DgFutureLab/satoyama-node/data/first_deployment/Battery Discharge.png

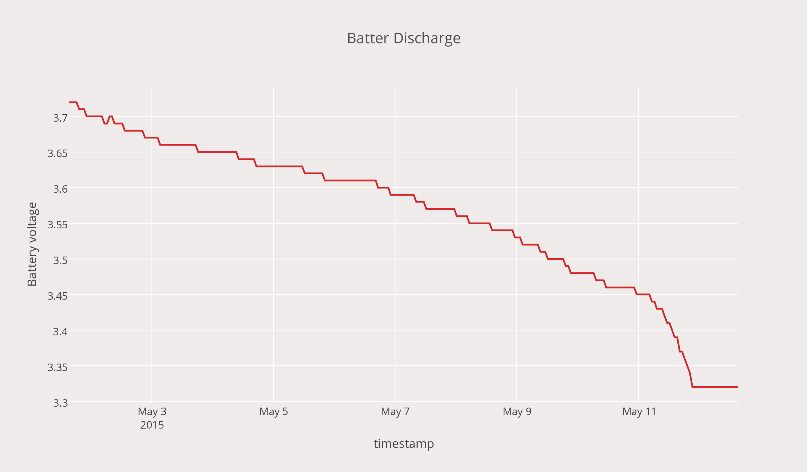
data/first_deployment/Battery Discharge.png
