DgFutureLab/satoyama-node/data/first_deployment/TechRice Alpha Field Water Level.png

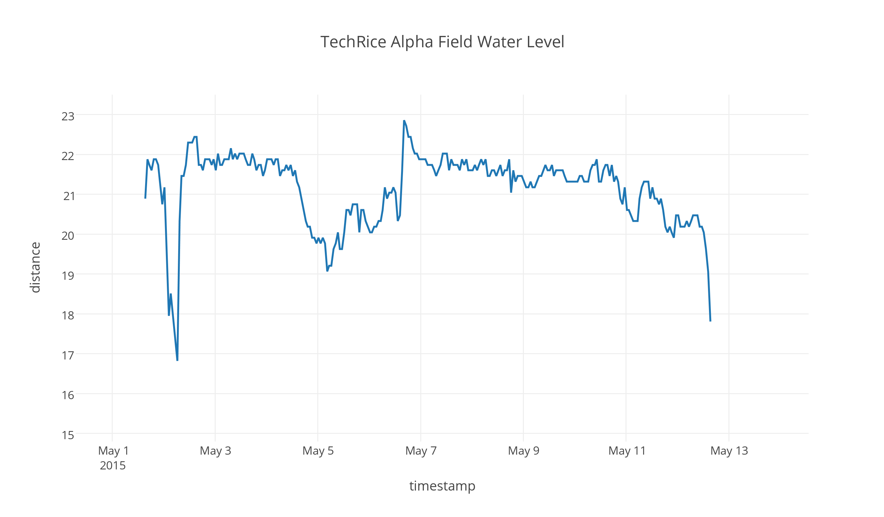
data/first_deployment/TechRice Alpha Field Water Level.png
