DgFutureLab/satoyama-node/hardware/range_finder/design1/simulation/TX/TX.asc

C1: cap; 0.01µF
Q1: npn; 2N2222
R1: res; 1.8k
R2: res; 1.8k
R3: res; 5.6k
R4: res; 470
R5: res; 220
R6: res; 400
U1: NE555
V5: voltage; 5
Named nets: 0, Vout, V5, Vpulse, e, b, c
.tran 0 200us 0 100us
.lib 2N2222.LIB
