DgFutureLab/satoyama-node/hardware/range_finder/design1/simulation/Vcc_pulse/main.asc

Q1: npn
R1: res; 470
R2: res; 5.6k
R3: res; 100
V1: voltage; PULSE(0 5 0 0.1us 0.1us 12.5us 25us 10)
Named nets: 0, Vout, Vin, V5
.tran 0 200us 0 100us
