DgFutureLab/satoyama-node/simulations/opamp_positive_bias.asc

R1: res; 10k
R2: res; 10k
U1: LT1006
V1: voltage; 5
V2: voltage; SINE(5 1 1000)
Vcc: voltage; 10
Named nets: 0, Vout, Vin
.tran 0 10m 0 1mu
