DgFutureLab/satoyama-node/simulations/basic_opamp.asc

R1: res; 10k
R2: res; 20k
U1: LT1006
V1: voltage; PWL(1m 0 1.001m 1 2m 1 2.001m 0)
Vss: voltage; 10
Named nets: 0, Vout, Vin
.tran 0 2.5m 0 1mu startup
