DgFutureLab/satoyama-node/simulations/transistors/sonar.asc

C1: cap; 6.8n
C2: cap; 33f
EN: voltage; PULSE(0 5 0 1u 1u 2m 4m 1)
mode: voltage; PULSE(0 5 0 1u 1u 0.5m 1m 1)
Q1: npn
Q2: npn
Q3: pnp
Q4: pnp
Q5: npn
Q6: npn
Q7: npn
Q8: npn
Q9: npn
Q10: npn
Q11: npn
R1: res; 1.5k
R2: res; 1.5k
R3: res; 1.5k
R4: res; 1.5k
R5: res; 10k
R6: res; 500
R7: res; 1.5k
R8: res; 10k
R9: res; 10k
R10: res; 100k
R11: res; 10k
R12: res; 10k
R13: res; 10k
R16: res; 10k
R17: res; 1.2k
R18: res; 1.2k
R19: res; 1.2k
R20: res; 10k
RX_pulse1: voltage; PULSE(0 50m 0.8m 0.1u 0.1u 25u 50u 10)
transducer: res; 100
TX_pulse: voltage; PULSE(0 5 0.25m 0.1u 0.1u 0.05m 0.1m 3)
U2: LT1006
Vcc: voltage; 5
Named nets: 0, Vcc, TX, TX_ON, RX_ON, TX+, TX-, RX+, RX-, Vout
.tran 0 3m 0 1u
