DgFutureLab/satoyama-node/simulations/transistors/active_lowpass.asc

C1: cap; 6.8n
C2: cap; 33p
R1: res; 1.2k
R2: res; 1.2k
R3: res; 1.2k
R4: res; 80k
U1: LT1006
V2: voltage; SINE(1 100m 40k)
Vcc: voltage; 5
Named nets: 0, Vcc, Vin, Vout
.tran 0 0.5m 0 1u
