DgFutureLab/satoyama-node/simulations/transistors/switched_TX.asc

mode: voltage; PULSE(0 5 0 1u 1u 0.5m 1m 5)
Q1: npn
Q2: npn
Q3: pnp
Q4: pnp
Q5: npn
Q6: npn
Q7: npn
Q8: npn
Q9: npn
Q10: npn
R1: res; 1.5k
R2: res; 1.5k
R3: res; 1.5k
R4: res; 1.5k
R5: res; 100
R6: res; 500
R7: res; 1.5k
R8: res; 10k
R9: res; 10k
R10: res; 100k
R11: res; 10k
R12: res; 10k
R13: res; 10k
R14: res; 5k
R15: res; 20k
R16: res; 10k
RX_pulse: voltage; PULSE(0 10m 0.5m 0.1u 0.1u 25u 50u 100)
TX_pulse: voltage; PULSE(0 5 0.25m 10u 10u 0.25m 0.5m 10)
U1: LT1006
V1: voltage; 5
V4: voltage; 1
Vcc2: voltage; 5
Named nets: 0, Vcc, TX, TX_ON, Vlog, RX_ON, TX+, TX-, piezo+, piezo-, RX+, RX-, Vout
.tran 0 1m 0 1u
