DgFutureLab/satoyama-node/simulations/transistors/HbridgeTX.asc

Q1: npn
Q2: npn
Q3: pnp
Q4: pnp
Q5: npn
R1: res; 1.5k
R2: res; 1.5k
R3: res; 1.5k
R4: res; 1.5k
R5: res; 100
R6: res; 500
R7: res; 1.5k
V1: voltage; 5
V2: voltage; PULSE(0 5 0.25m 10u 10u 0.25m 1)
Named nets: 0, Vcc, TX
.tran 0 1m 0 1u
