DgFutureLab/satoyama-node/simulations/transistors/circuit_switch.asc

Q1: npn
Q2: npn
Q3: npn
R1: res; 10k
R2: res; 10k
R3: res; 1k
R4: res; 100k
R5: res; 100k
R6: res; 10k
R7: res; 1k
R8: res; 100k
R9: res; 10k
Vcc1: voltage; 5
Vcc: voltage; 10
Vpin: voltage; PULSE(0 5 0.25m 10u 10u 0.25m 1)
Named nets: 0, EN, Vcc, Vlog, notEN
.tran 0 1m 0 1u
