DgFutureLab/satoyama-node/hardware/range_finder/design2/rxtx.sch

## EAGLE design hardware/range_finder/design2/rxtx.sch (2015-09-01)

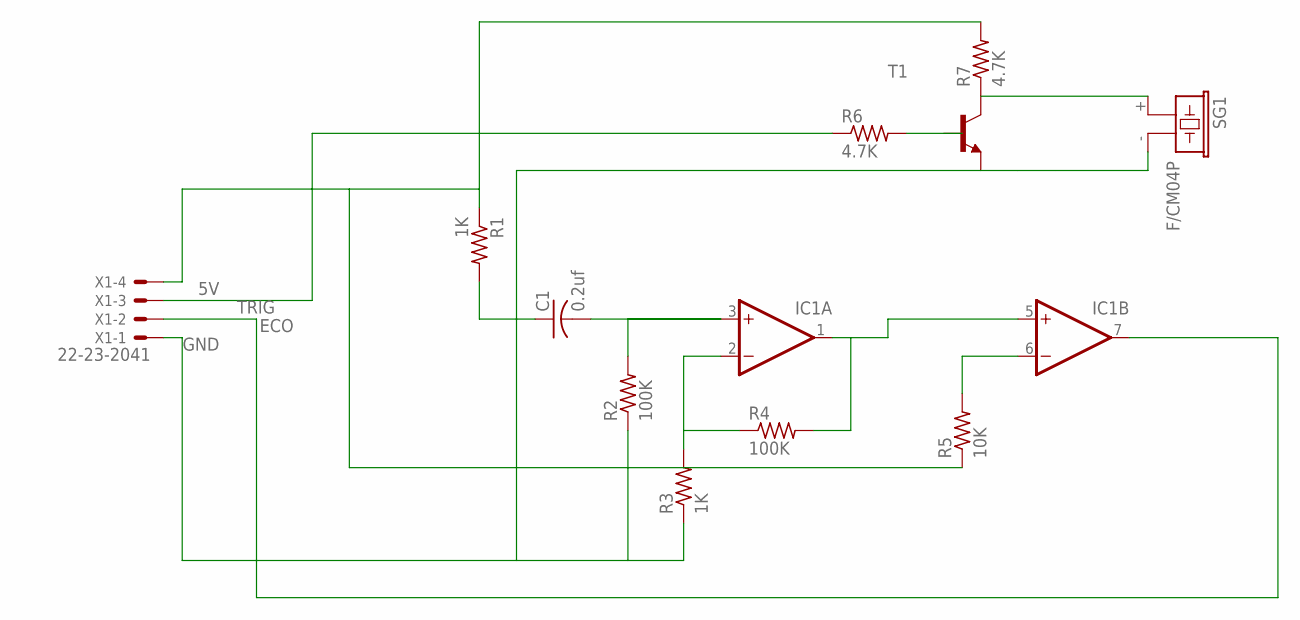
[picture p16: schematic rxtx.sch]

Parts:
C1: 0.2uf; C0805
IC1: 2AMP_P8+4D; SO08
R1, R3: 1K; R0805
R2, R4: 100K; R0805
R5: 10K; R0805
R6, R7: 4.7K; R0805
SG1: F/CM04P
T1: -NPN-SOT23-EBC; SOT23-EBC
X1: 22-23-2041

Connections:
5V: R1.1, R5.1, R7.2, X1.4
ECO: IC1.7 (OUT), X1.2
GND: R2.1, R3.1, SG1.- (2), T1.E, X1.1
unnamed: C1.2, IC1.3 (+IN), R2.2
unnamed: C1.1, R1.2
unnamed: IC1.2 (-IN), R3.2, R4.1
unnamed: IC1.1 (OUT), IC1.5 (+IN), R4.2
unnamed: IC1.6 (-IN), R5.2
unnamed: R7.1, SG1.+ (1), T1.C
TRIG: R6.1, X1.3
