DgFutureLab/satoyama-node/hardware/range_finder/design1/Schematics/Transmitter.sch

## EAGLE design hardware/range_finder/design1/Schematics/Transmitter.sch (2015-06-08)

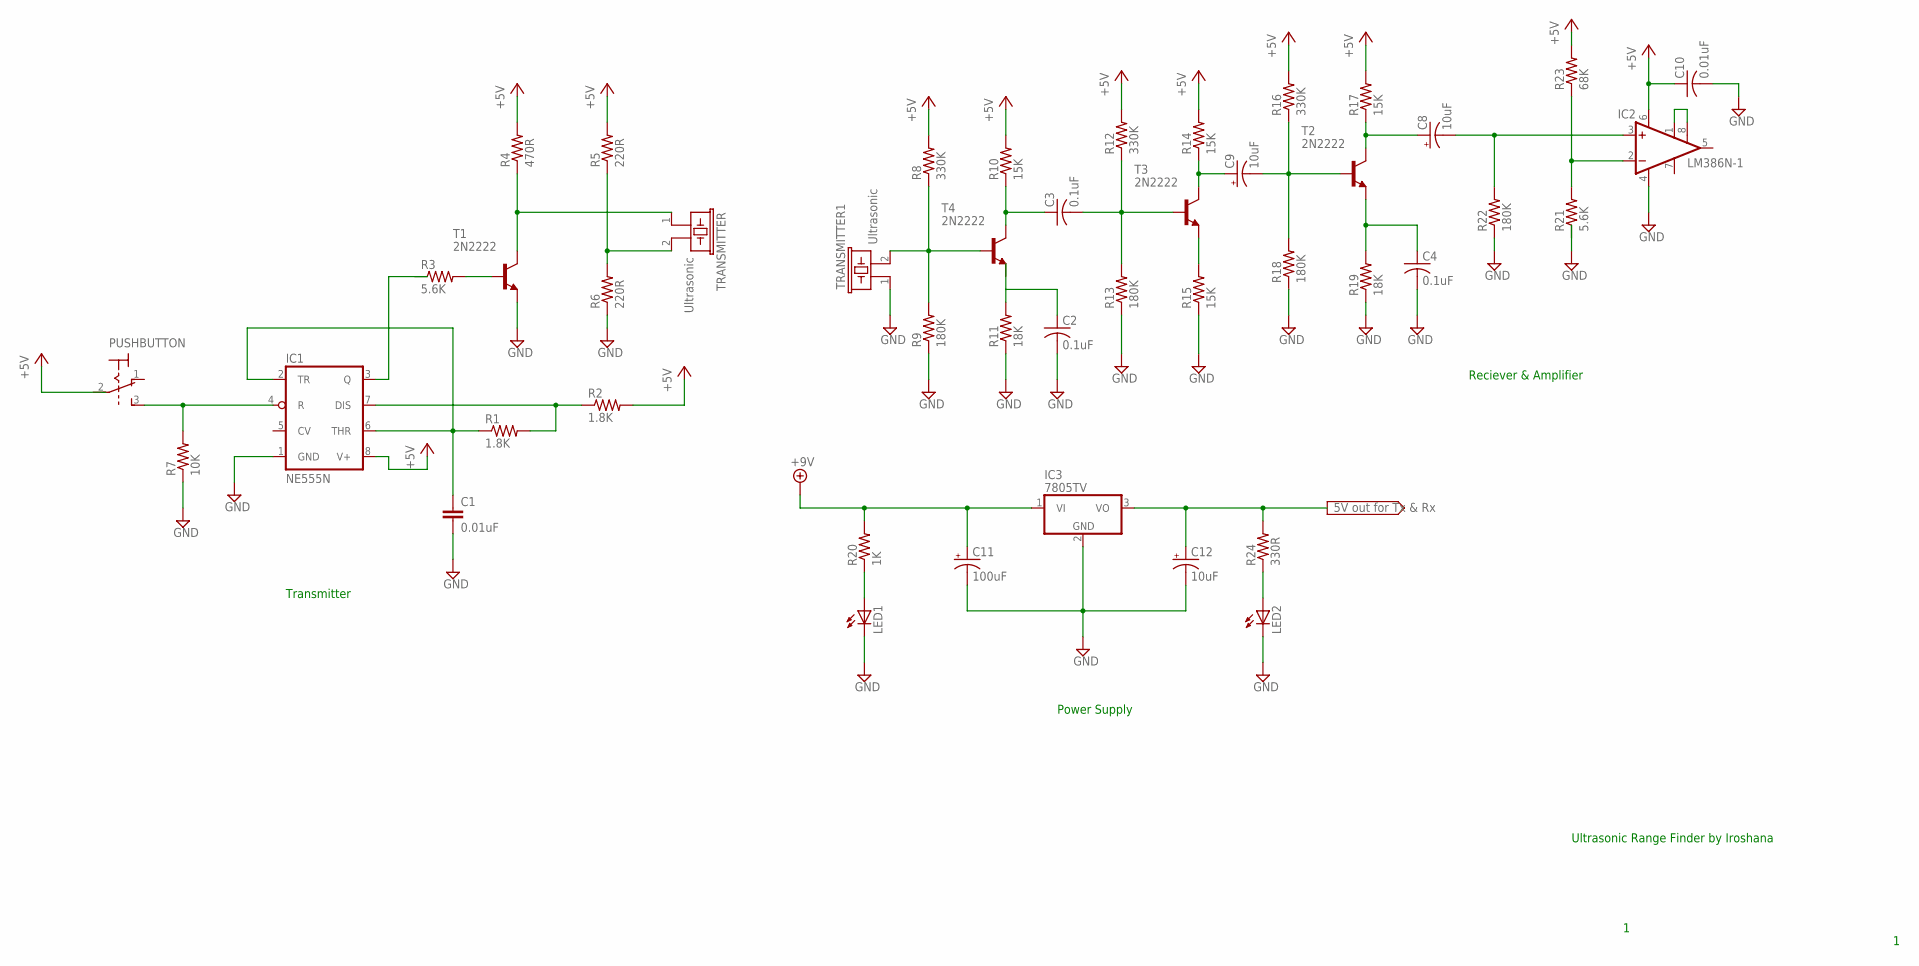
[picture p17: schematic Transmitter.sch]

Parts:
C1: 0.01uF; C2.5-2
C2, C3, C4: 0.1uF; C025-025X050
C8, C9, C12: 10uF; E2,5-6
C10: 0.01uF; C025-025X050
C11: 100uF; E2,5-6
IC1: NE555N; DIL08-ROUND
IC2: LM386N-1; DIL08
IC3: 7805TV; TO220V
LED1, LED2: LED5MM
PUSHBUTTON: M9040P2
R1, R2: 1.8K; 0207/10
R3, R21: 5.6K; 0207/10
R4: 470R; 0207/10
R5, R6: 220R; 0207/10
R7: 10K; 0207/10
R8, R12, R16: 330K; 0207/10
R9, R13, R18, R22: 180K; 0207/10
R10, R14, R15, R17: 15K; 0207/10
R11, R19: 18K; 0207/10
R20: 1K; 0207/10
R23: 68K; 0207/10
R24: 330R; 0207/10
T1, T2, T3, T4: 2N2222; TO92-EBC-OVAL
TRANSMITTER, TRANSMITTER1: Ultrasonic; EFBRD22C41

Connections:
+5V: C10.1, IC1.8 (V+), IC2.6 (VS), R2.2, R4.2, R5.2, R8.2, R10.2, R12.2, R14.2, R16.2, R17.2, R23.2
+9V: C11.+, IC3.1 (VI), R20.2
CONN: C1.1, IC1.2 (TR), IC1.6 (THR), R1.1
GND: C1.2, C2.2, C4.2, C10.2, C11.-, C12.-, IC1.1 (GND), IC2.4 (GND), IC3.2 (GND), LED1.K (C), LED2.K (C), R6.1, R7.1, R9.1, R11.1, R13.1, R15.1, R18.1, R19.1, R22.1, T1.E, TRANSMITTER1.1
unnamed: R3.2, T1.B
unnamed: R4.1, T1.C, TRANSMITTER.1
unnamed: R5.1, R6.2, TRANSMITTER.2
unnamed: IC1.4 (R), PUSHBUTTON.3 (S), R7.2
unnamed: R8.1, R9.2, T4.B, TRANSMITTER1.2
unnamed: C2.1, R11.2
unnamed: C3.2, R12.1, R13.2, T3.B
unnamed: IC1.7 (DIS), R1.2, R2.1
unnamed: C9.+, R14.1, T3.C
unnamed: R15.2, T3.E
unnamed: C9.-, R16.1, R18.2, T2.B
unnamed: C4.1, R19.2, T2.E
unnamed: C8.+, R17.1, T2.C
unnamed: C8.-, IC2.3 (+IN), R22.2
unnamed: IC2.2 (-IN), R21.2, R23.1
unnamed: IC2.1 (GAIN), IC2.8 (GAIN)
unnamed: C3.1, R10.1, T4.C
unnamed: C12.+, IC3.3 (VO), R24.2
unnamed: LED1.A, R20.1
unnamed: LED2.A, R24.1

Notes on the sheet:
Power Supply
Reciever & Amplifier
Transmitter
Ultrasonic Range Finder by Iroshana
